GeorgeGrasu/Proiect_TSC/Images/Capture1.PNG

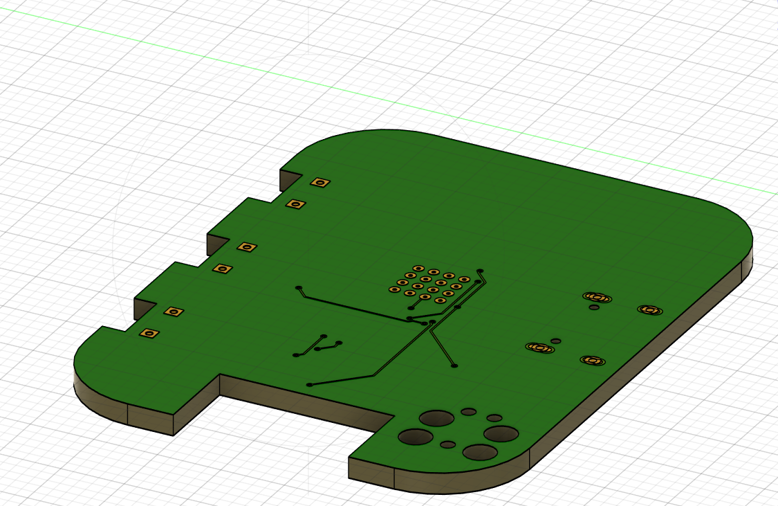
Images/Capture1.PNG
