GeorgeGrasu/Proiect_TSC/Images/Capture2.PNG

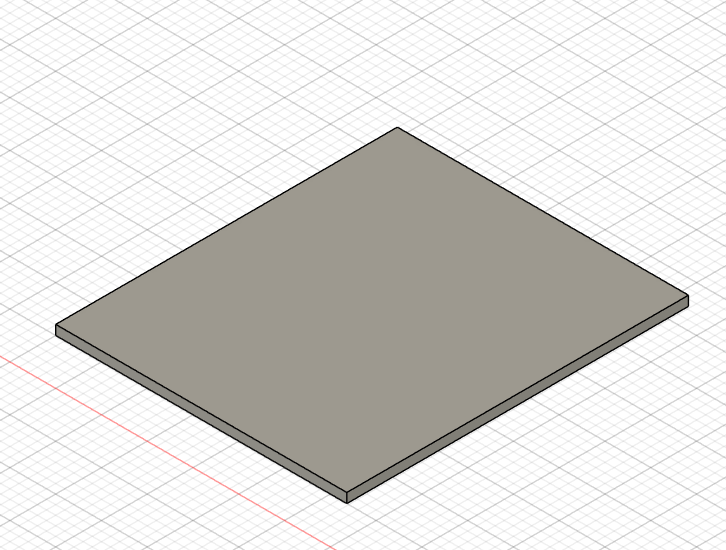
Images/Capture2.PNG
