GeorgeGrasu/Proiect_TSC/Images/Capture4 (2).PNG

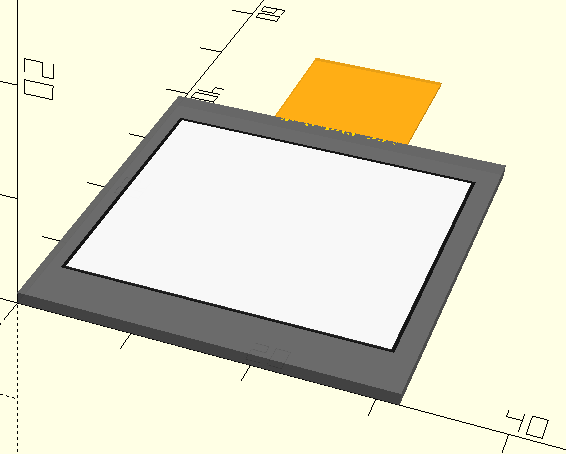
Images/Capture4 (2).PNG
