GeorgeGrasu/Proiect_TSC/Images/Capture7.PNG

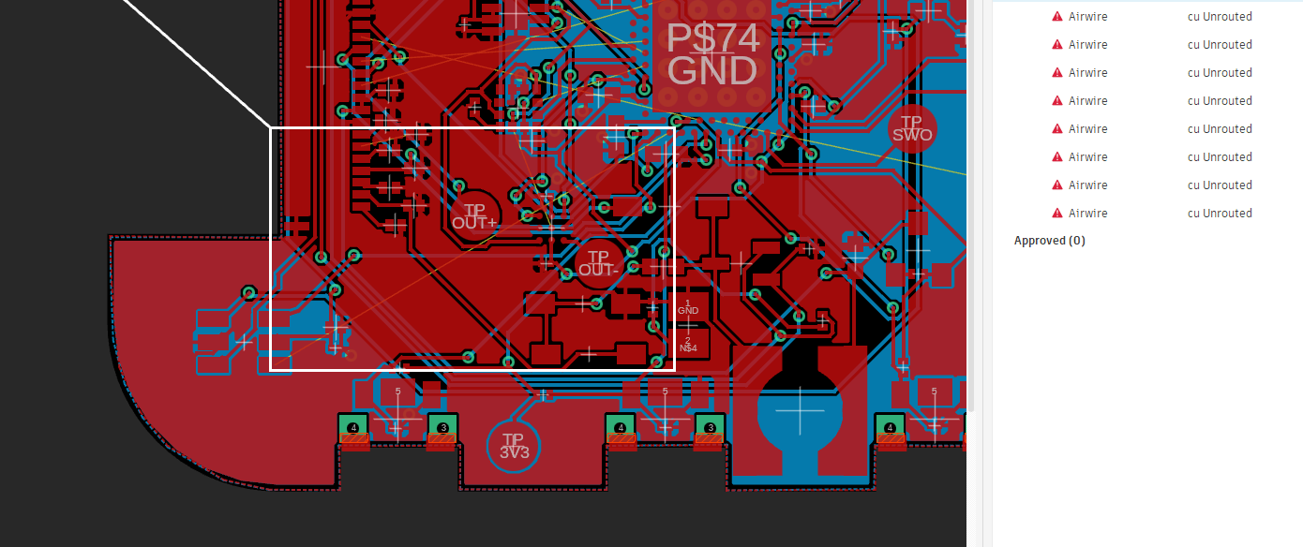
Images/Capture7.PNG
