GeorgeGrasu/Proiect_TSC/Images/Capture8.PNG

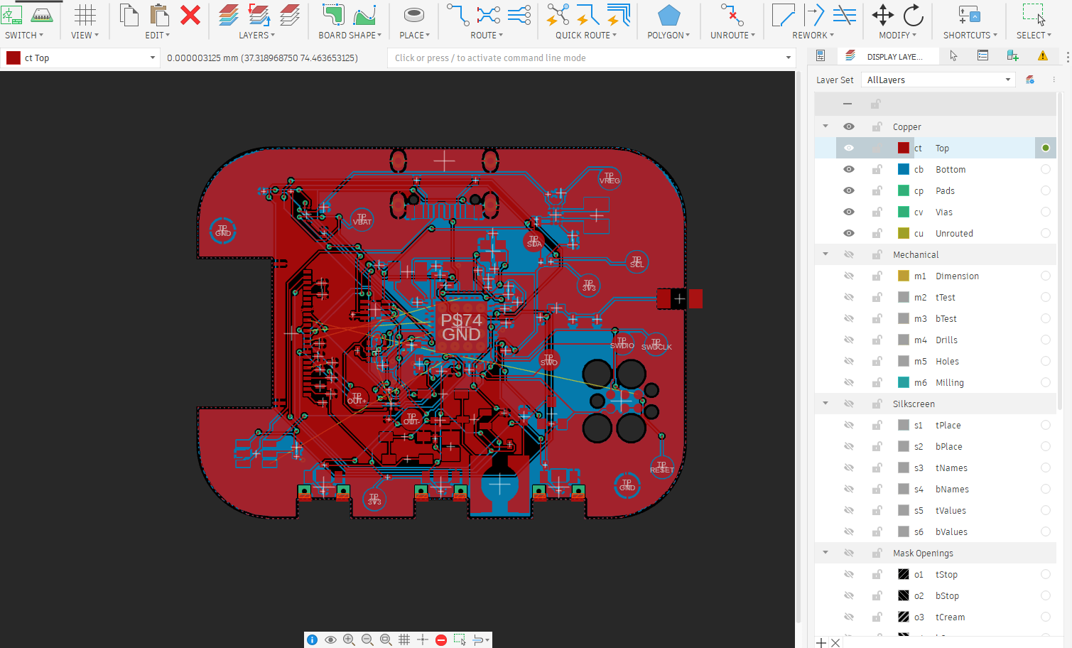
Images/Capture8.PNG
