GeorgeGrasu/Proiect_TSC/Images/Capture9.PNG

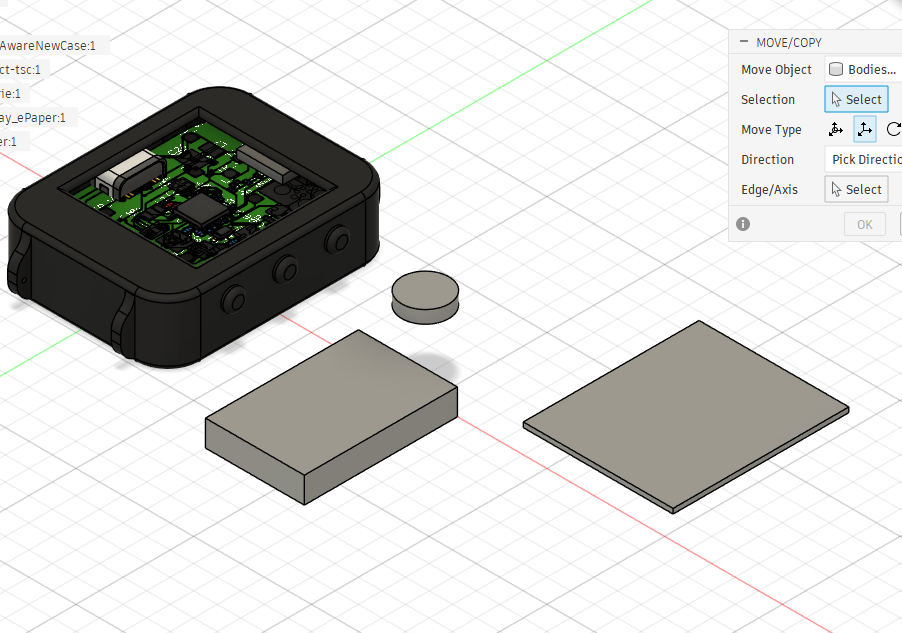
Images/Capture9.PNG
