GeorgeGrasu/Proiect_TSC/Images/Capture.PNG

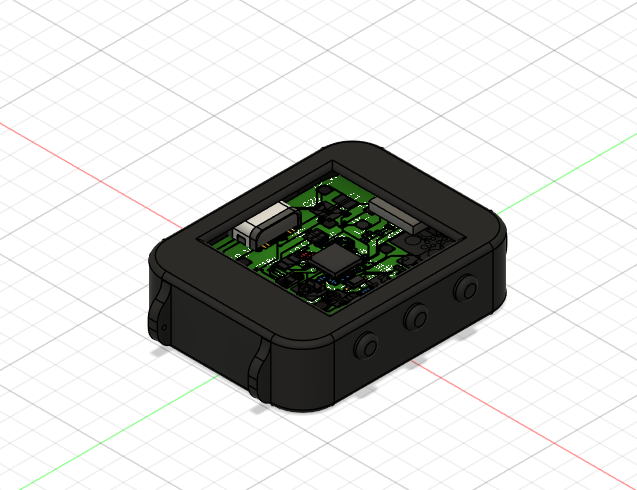
Images/Capture.PNG
