GeorgeGrasu/Proiect_TSC/Images/assembly_exploded.png

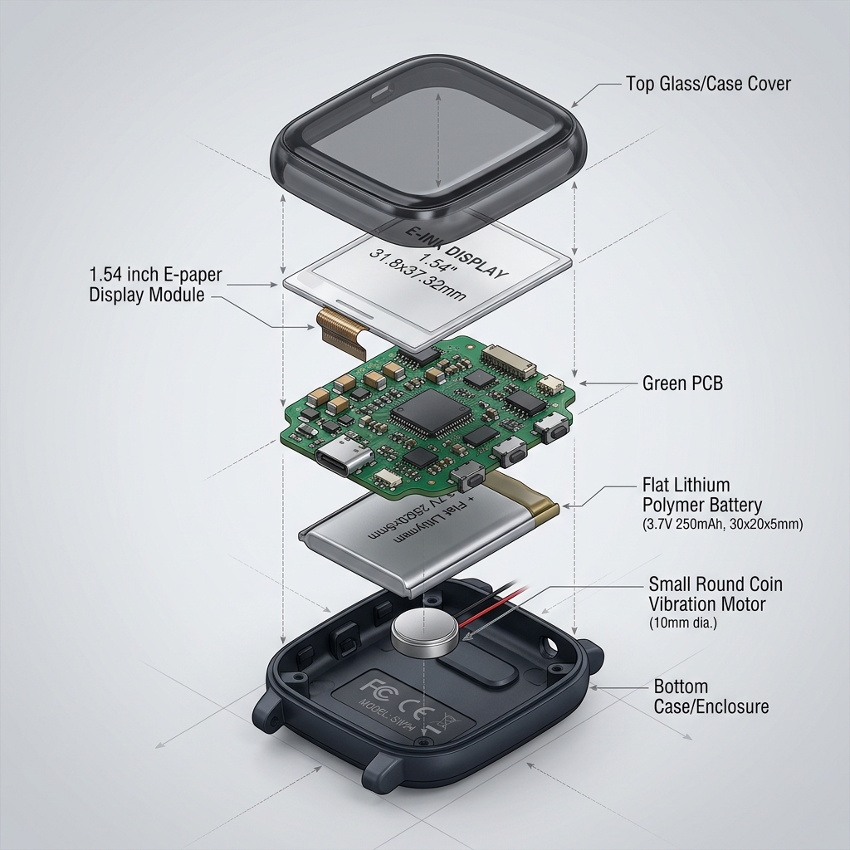
Images/assembly_exploded.png
